kauzerei/FabLabRocker/3d_print/BOSL2/images/metaball_demo.gif

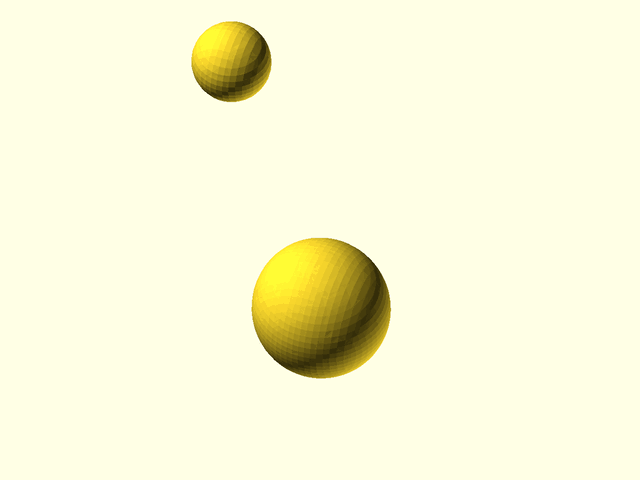
3d_print/BOSL2/images/metaball_demo.gif
